idiot-io/nanoRF/examples/simple-tx/simple-tx.ino

// SimpleTx - the master or the transmitter

#include "switchPin.h"
#define FLASH_PIN 4
#define FLASH_GND_PIN 5
#define TRIG_PIN 2

#include <SPI.h>
#include <nRF24L01.h>
#include <RF24.h>


#define CE_PIN   7
#define CSN_PIN 8

const byte slaveAddress[5] = {'R', 'x', 'A', 'A', 'A'};


RF24 radio(CE_PIN, CSN_PIN); // Create a Radio

char dataToSend[10] = "Message 0";
char txNum = '0';


unsigned long currentMillis;
unsigned long prevMillis;
unsigned long txIntervalMillis = 33; // send once per second
bool state;

void setup() {

  Serial.begin(115200);
  Serial.println("TX...");
  //attachInterrupt(digitalPinToInterrupt(TRIG_PIN), blink, RISING);

  pinMode(FLASH_PIN, OUTPUT);
  digitalWrite(FLASH_PIN, LOW);
  pinMode(FLASH_GND_PIN, OUTPUT);
  digitalWrite(FLASH_GND_PIN, LOW);

  radio.begin();
  radio.setDataRate( RF24_250KBPS );
  radio.setRetries(3, 5); // delay, count
  radio.openWritingPipe(slaveAddress);
}

//====================

void loop() {
  currentMillis = millis();
  if (currentMillis - prevMillis >= txIntervalMillis) {
    // send();
    // flashOut();
    switchOn<FLASH_PIN>();
    radio.write( &dataToSend, sizeof(dataToSend) );
    switchOff<FLASH_PIN>();
    prevMillis = millis();
  }
}

//====================

void flashOut() {
  if (state) {
    switchOn<FLASH_PIN>();
    radio.write( &dataToSend, sizeof(dataToSend) );
    switchOff<FLASH_PIN>();
    state = 0;
  }
}

void blink() {
  state = 1;
}

void send() {

  bool rslt;
  rslt = radio.write( &dataToSend, sizeof(dataToSend) );
  // Always use sizeof() as it gives the size as the number of bytes.
  // For example if dataToSend was an int sizeof() would correctly return 2

  Serial.print("Data Sent ");
  Serial.print(dataToSend);
  if (rslt) {
    Serial.println("  Acknowledge received");
    updateMessage();
  }
  else {
    Serial.println("  Tx failed");
  }
}

//================

void updateMessage() {
  // so you can see that new data is being sent
  txNum += 1;
  if (txNum > '9') {
    txNum = '0';
  }
  dataToSend[8] = txNum;
}
